linshuqin329/UPS-Lite/2.13_EPD_for_UPS_Lite/images/2.13_EPD_for_UPS_Lite_1.jpg

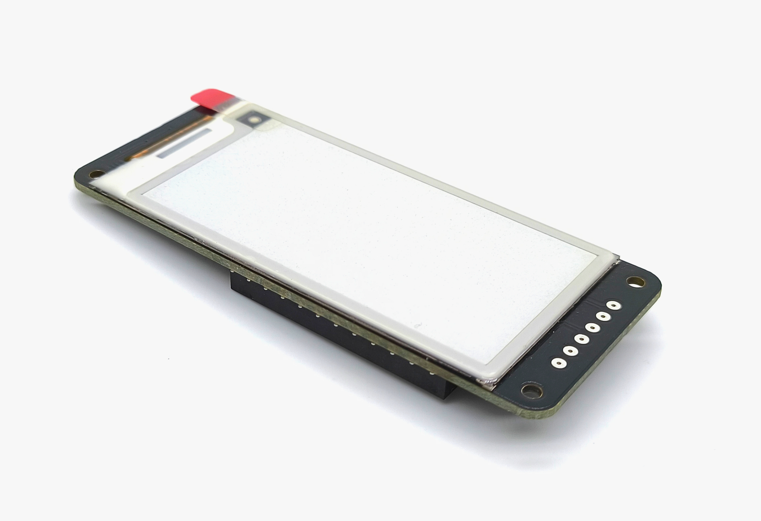
2.13_EPD_for_UPS_Lite/images/2.13_EPD_for_UPS_Lite_1.jpg
