linshuqin329/UPS-Lite/2.13_EPD_for_UPS_Lite/images/2.13_EPD_for_UPS_Lite_2.jpg

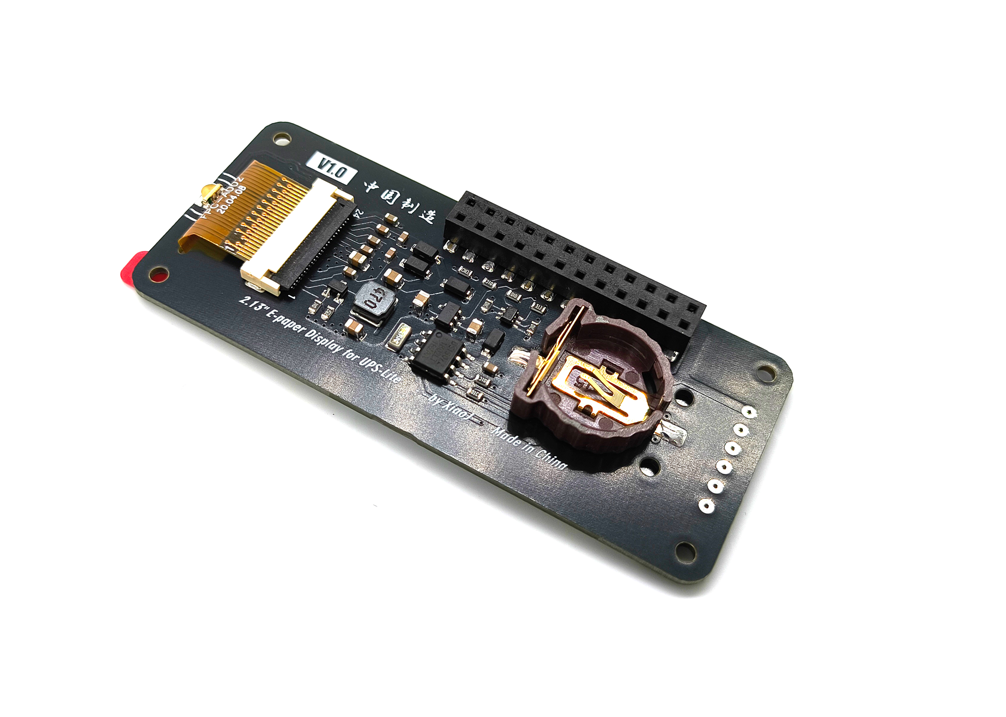
2.13_EPD_for_UPS_Lite/images/2.13_EPD_for_UPS_Lite_2.jpg
