linshuqin329/UPS-Lite/UPS-Lite_Case/UPS-Lite_EPD_Antenna_Case/images/UPS-Lite_EPD_Antenna_Case_1.jpg

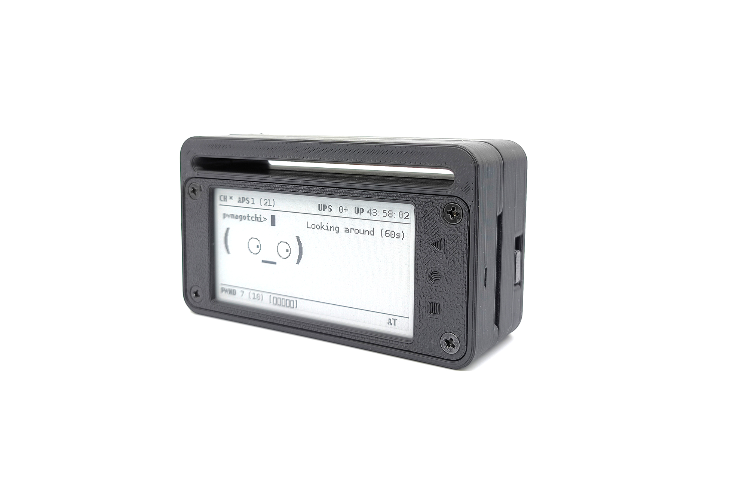
UPS-Lite_Case/UPS-Lite_EPD_Antenna_Case/images/UPS-Lite_EPD_Antenna_Case_1.jpg
