linshuqin329/UPS-Lite/UPS-Lite_Case/UPS-Lite_EPD_Case/images/UPS-Lite_EPD_Case_3.jpg

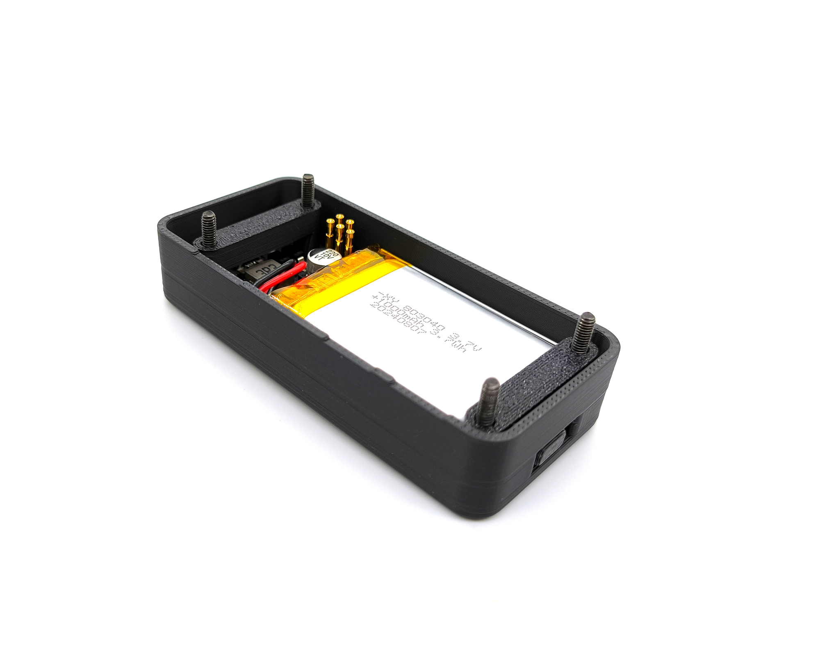
UPS-Lite_Case/UPS-Lite_EPD_Case/images/UPS-Lite_EPD_Case_3.jpg
